Soundpauli/NI404/files.h

const String usedFiles[13] = { "samples/_1.wav",
                               "samples/_2.wav",
                               "samples/_3.wav",
                               "samples/_4.wav",
                               "samples/_5.wav",
                               "samples/_6.wav",
                               "samples/_7.wav",
                               "samples/_8.wav",
                               "samples/_9.wav",
                               "samples/_10.wav",
                               "samples/_11.wav",
                               "samples/_12.wav",
                               "samples/_13.wav" };

const int number[10][24][2] = {
  { { 1, 1 }, { 2, 1 }, { 3, 1 }, { 4, 1 }, { 4, 2 }, { 1, 3 }, { 4, 3 }, { 1, 4 }, { 4, 4 }, { 1, 5 }, { 4, 5 }, { 1, 6 }, { 4, 6 }, { 1, 7 }, { 4, 7 }, { 1, 8 }, { 1, 9 }, { 2, 9 }, { 3, 9 }, { 4, 9 }, { 1, 2 }, { 4, 8 }, { 4, 8 }, { 4, 8 } },  //0
  { { 3, 1 }, { 2, 2 }, { 3, 2 }, { 1, 3 }, { 3, 3 }, { 3, 4 }, { 3, 5 }, { 3, 6 }, { 3, 7 }, { 3, 8 }, { 2, 9 }, { 3, 9 }, { 4, 9 }, { 4, 9 }, { 4, 9 }, { 4, 9 }, { 4, 9 }, { 4, 9 }, { 4, 9 }, { 4, 9 }, { 4, 9 }, { 4, 9 }, { 4, 9 }, { 4, 9 } },  //1
  { { 1, 1 }, { 2, 1 }, { 3, 1 }, { 4, 1 }, { 4, 2 }, { 4, 3 }, { 4, 4 }, { 1, 5 }, { 2, 5 }, { 3, 5 }, { 4, 5 }, { 1, 6 }, { 1, 7 }, { 1, 8 }, { 1, 9 }, { 2, 9 }, { 3, 9 }, { 4, 9 }, { 1, 2 }, { 4, 8 }, { 4, 8 }, { 4, 8 }, { 4, 8 }, { 4, 8 } },  //2
  { { 1, 1 }, { 2, 1 }, { 3, 1 }, { 4, 1 }, { 4, 2 }, { 4, 3 }, { 4, 4 }, { 2, 5 }, { 3, 5 }, { 4, 5 }, { 4, 6 }, { 4, 7 }, { 4, 8 }, { 1, 9 }, { 2, 9 }, { 3, 9 }, { 4, 9 }, { 4, 9 }, { 4, 9 }, { 4, 9 }, { 4, 9 }, { 4, 9 }, { 4, 9 }, { 4, 9 } },  //3
  { { 1, 1 }, { 4, 1 }, { 1, 2 }, { 4, 2 }, { 1, 3 }, { 4, 3 }, { 1, 4 }, { 4, 4 }, { 1, 5 }, { 2, 5 }, { 3, 5 }, { 4, 5 }, { 4, 6 }, { 4, 7 }, { 4, 8 }, { 4, 9 }, { 4, 9 }, { 4, 9 }, { 4, 9 }, { 4, 9 }, { 4, 9 }, { 4, 9 }, { 4, 9 }, { 4, 9 } },  //4
  { { 1, 1 }, { 2, 1 }, { 3, 1 }, { 4, 1 }, { 1, 2 }, { 1, 3 }, { 1, 4 }, { 1, 5 }, { 2, 5 }, { 3, 5 }, { 4, 5 }, { 4, 6 }, { 4, 7 }, { 4, 8 }, { 1, 9 }, { 2, 9 }, { 3, 9 }, { 4, 9 }, { 4, 9 }, { 4, 9 }, { 4, 9 }, { 4, 9 }, { 4, 9 }, { 4, 9 } },  //5
  { { 1, 1 }, { 2, 1 }, { 3, 1 }, { 4, 1 }, { 1, 2 }, { 1, 3 }, { 1, 4 }, { 1, 5 }, { 2, 5 }, { 3, 5 }, { 4, 5 }, { 1, 6 }, { 4, 6 }, { 1, 7 }, { 4, 7 }, { 1, 8 }, { 4, 8 }, { 1, 9 }, { 2, 9 }, { 3, 9 }, { 4, 9 }, { 4, 9 }, { 4, 9 }, { 4, 9 } },  //6
  { { 1, 1 }, { 2, 1 }, { 3, 1 }, { 4, 1 }, { 4, 2 }, { 4, 3 }, { 4, 4 }, { 4, 5 }, { 4, 6 }, { 4, 7 }, { 4, 8 }, { 4, 9 }, { 1, 2 }, { 1, 2 }, { 1, 2 }, { 1, 2 }, { 1, 2 }, { 1, 2 }, { 1, 2 }, { 1, 2 }, { 1, 2 }, { 1, 2 }, { 1, 2 }, { 1, 2 } },  //7
  { { 1, 1 }, { 2, 1 }, { 3, 1 }, { 4, 1 }, { 4, 2 }, { 1, 3 }, { 4, 3 }, { 1, 4 }, { 4, 4 }, { 1, 5 }, { 2, 5 }, { 3, 5 }, { 4, 5 }, { 1, 6 }, { 4, 6 }, { 1, 7 }, { 4, 7 }, { 1, 8 }, { 1, 9 }, { 2, 9 }, { 3, 9 }, { 4, 9 }, { 1, 2 }, { 4, 8 } },  //8
  { { 1, 1 }, { 2, 1 }, { 3, 1 }, { 4, 1 }, { 4, 2 }, { 1, 3 }, { 4, 3 }, { 1, 4 }, { 4, 4 }, { 1, 5 }, { 2, 5 }, { 3, 5 }, { 4, 5 }, { 4, 6 }, { 4, 7 }, { 1, 9 }, { 2, 9 }, { 3, 9 }, { 4, 9 }, { 1, 2 }, { 4, 8 }, { 4, 8 }, { 4, 8 }, { 4, 8 } }
};

const int logo[102][2] = {
  { 1, 2 }, { 2, 2 }, { 3, 2 }, { 4, 2 }, { 5, 2 }, { 6, 2 }, { 7, 2 }, { 8, 2 }, { 9, 2 }, { 10, 2 }, { 11, 2 }, { 12, 2 }, { 13, 2 }, { 14, 2 }, { 15, 2 }, { 15, 3 }, { 15, 4 }, { 15, 5 }, { 15, 6 }, { 15, 7 }, { 15, 8 }, { 14, 8 }, { 13, 8 }, { 12, 8 }, { 11, 8 }, { 11, 9 }, { 11, 10 }, { 11, 11 }, { 11, 12 }, { 11, 13 }, { 11, 14 }, { 10, 14 }, { 9, 14 }, { 9, 13 }, { 9, 12 }, { 9, 11 }, { 9, 10 }, { 9, 9 }, { 9, 8 }, { 9, 7 }, { 9, 6 }, { 9, 5 }, { 9, 4 }, { 8, 4 }, { 7, 4 }, { 6, 4 }, { 5, 4 }, { 4, 4 }, { 3, 4 }, { 3, 5 }, { 3, 6 }, { 3, 7 }, { 4, 7 }, { 5, 7 }, { 6, 7 }, { 7, 7 }, { 7, 8 }, { 7, 9 }, { 7, 10 }, { 7, 11 }, { 7, 12 }, { 7, 13 }, { 7, 14 }, { 6, 14 }, { 5, 14 }, { 4, 14 }, { 3, 14 }, { 2, 14 }, { 1, 14 }, { 1, 13 }, { 1, 12 }, { 2, 12 }, { 3, 12 }, { 4, 12 }, { 5, 12 }, { 5, 11 }, { 5, 10 }, { 5, 9 }, { 4, 9 }, { 3, 9 }, { 2, 9 }, { 1, 9 }, { 1, 8 }, { 1, 7 }, { 1, 6 }, { 1, 5 }, { 1, 4 }, { 1, 3 }, { 11, 4 }, { 12, 4 }, { 13, 4 }, { 13, 5 }, { 13, 6 }, { 12, 6 }, { 11, 6 }, { 11, 5 }

};

const int icon_samplepack[18][2] = { { 2, 1 }, { 2, 2 }, { 3, 2 }, { 2, 3 }, { 2, 4 }, { 4, 4 }, { 1, 5 }, { 2, 5 }, { 4, 5 }, { 5, 5 }, { 1, 6 }, { 2, 6 }, { 4, 6 }, { 4, 7 }, { 3, 8 }, { 4, 8 }, { 3, 9 }, { 4, 9 } };
const int icon_sample[19][2] = { { 3, 1 }, { 3, 2 }, { 3, 3 }, { 4, 3 }, { 3, 5 }, { 4, 2 }, { 5, 3 }, { 3, 4 }, { 3, 5 }, { 3, 6 }, { 1, 7 }, { 2, 7 }, { 3, 7 }, { 1, 8 }, { 2, 8 }, { 3, 8 }, { 1, 9 }, { 2, 9 }, { 3, 9 } };
const int icon_loadsave[20][2] = { { 3, 1 }, { 3, 2 }, { 3, 3 }, { 3, 4 }, { 1, 5 }, { 2, 5 }, { 3, 5 }, { 4, 5 }, { 5, 5 }, { 2, 6 }, { 3, 6 }, { 4, 6 }, { 3, 7 }, { 1, 8 }, { 5, 8 }, { 1, 9 }, { 2, 9 }, { 3, 9 }, { 4, 9 }, { 5, 9 } };
const int icon_bpm[38][2] = { { 2, 11 }, { 3, 11 }, { 4, 11 }, { 7, 11 }, { 8, 11 }, { 9, 11 }, { 11, 11 }, { 15, 11 }, { 2, 12 }, { 4, 12 }, { 7, 12 }, { 9, 12 }, { 11, 12 }, { 12, 12 }, { 14, 12 }, { 15, 12 }, { 2, 13 }, { 3, 13 }, { 4, 13 }, { 5, 13 }, { 7, 13 }, { 8, 13 }, { 9, 13 }, { 11, 13 }, { 13, 13 }, { 15, 13 }, { 2, 14 }, { 5, 14 }, { 7, 14 }, { 11, 14 }, { 15, 14 }, { 2, 15 }, { 3, 15 }, { 4, 15 }, { 5, 15 }, { 7, 15 }, { 11, 15 }, { 15, 15 } };
const int helper_load[3][2] = { { 1, 15 }, { 2, 15 }, { 3, 15 } };
const int helper_folder[5][2] = { { 6, 13 }, { 6, 14 }, { 6, 15 }, { 7, 14 }, { 7, 15 } };
const int helper_seek[2][2] = { { 10, 15 }, { 10, 14 } };

const int helper_vol[5][2] = { { 9, 13 }, { 11, 13 }, { 10, 15 }, { 9, 14 }, { 11, 14 } };
//for 3 encoders:
const int helper_vol2[5][2] = { { 6, 13 }, { 8, 13 }, { 7, 15 }, { 6, 14 }, { 8, 14 } };

const int helper_bpm[7][2] = { { 13, 13 }, { 13, 14 }, { 13, 15 }, { 14, 14 }, { 15, 14 }, { 14, 15 }, { 15, 15 } };


const int helper_save[3][2] = { { 5, 15 }, { 6, 15 }, { 7, 15 } };
const int helper_select[3][2] = { { 13, 15 }, { 14, 15 }, { 15, 15 } };

const int noSD[48][2] = { { 2, 4 }, { 3, 4 }, { 4, 4 }, { 5, 4 }, { 7, 4 }, { 8, 4 }, { 9, 4 }, { 12, 4 }, { 13, 4 }, { 14, 4 }, { 15, 4 }, { 2, 5 }, { 5, 5 }, { 7, 5 }, { 9, 5 }, { 10, 5 }, { 12, 5 }, { 15, 5 }, { 2, 6 }, { 7, 6 }, { 10, 6 }, { 15, 6 }, { 2, 7 }, { 3, 7 }, { 4, 7 }, { 5, 7 }, { 7, 7 }, { 10, 7 }, { 13, 7 }, { 14, 7 }, { 15, 7 }, { 5, 8 }, { 7, 8 }, { 10, 8 }, { 13, 8 }, { 2, 9 }, { 5, 9 }, { 7, 9 }, { 9, 9 }, { 10, 9 }, { 2, 10 }, { 3, 10 }, { 4, 10 }, { 5, 10 }, { 7, 10 }, { 8, 10 }, { 9, 10 }, { 13, 10 } };
