Soundpauli/NI404/colors.h

const CRGB col_Folder[] = {CRGB(30, 0, 0), CRGB(40, 60, 20), CRGB(20, 25, 4), CRGB(3, 30, 1), CRGB(0, 20, 0), CRGB(3, 30, 10), CRGB(0, 20, 15), CRGB(0, 0, 20), CRGB(10, 0, 20), CRGB(20, 0, 20), CRGB(50, 0, 0), CRGB(20, 0, 0), CRGB(40, 10, 0), CRGB(20, 20, 0), CRGB(0, 0, 10)};
const CRGB col[] = {
  CRGB(0, 0, 0),    //empty
  
  CRGB(40, 0, 0),   //1
  CRGB(0, 0, 40),   //2
  CRGB(40, 40, 0),  //3
  CRGB(0, 60, 0),   //4
  CRGB(40, 0, 20),  //5
  
  CRGB(10, 20, 0),  // 6
  CRGB(60, 10, 0),  //7
  CRGB(0, 40, 30),  //8  
  
  
  CRGB(0, 0, 0),  //
  CRGB(0, 0, 0),   //
  CRGB(0, 0, 0),   //
  CRGB(0, 0, 0),  //
  
  CRGB(17, 5, 35),  //13
  CRGB(20, 20, 20)};  // 14 SYNTH
